luque667788/dsp_guitar_effect_pedal/guitar_pedal_software/Src/dsp.c

#include "dsp.h"
#include <stdint.h>

__attribute__((section(".dma_buffer"))) uint16_t delayBuffer[Delay];
uint16_t delayWriteIndex = 0;

void dsp_algorithm(uint16_t *input, uint16_t *output, int startindex,
                   int endindex) {

  const int32_t ADC_MID = 32768;
  const int32_t DAC_MID = 2048;

  for (int i = startindex; i < endindex; i++) {
    int32_t dry = ((int32_t)input[i] - ADC_MID) >> 4;

    uint16_t readIndex = (delayWriteIndex + 1) % Delay;
    int32_t delayed = (int32_t)delayBuffer[readIndex] - DAC_MID;

    int32_t fb = dry + (delayed / 2);
    if (fb >  2047) fb =  2047;
    if (fb < -2048) fb = -2048;
    delayBuffer[delayWriteIndex] = (uint16_t)(DAC_MID + fb);
    delayWriteIndex = (delayWriteIndex + 1) % Delay;

    int32_t out = DAC_MID + dry + (delayed * 6 / 10);
    if (out > 4095) out = 4095;
    if (out < 0)    out = 0;

    output[i] = (uint16_t)out;
  }
}
