luque667788/dsp_guitar_effect_pedal/guitar_pedal_software/Inc/dsp.h

#ifndef DSP_H
#define DSP_H

#include <stdint.h>


#ifdef __cplusplus
extern "C" {
#endif

#define Delay 14400

void dsp_example_function(void);

void dsp_algorithm(uint16_t *input, uint16_t *output, int startindex, int endindex);



#ifdef __cplusplus
}
#endif

#endif // DSP_H
